haktar65/quarter-tone-keyboard/docs/CAD/QTKB-blocks/V2BL-Layout.stp

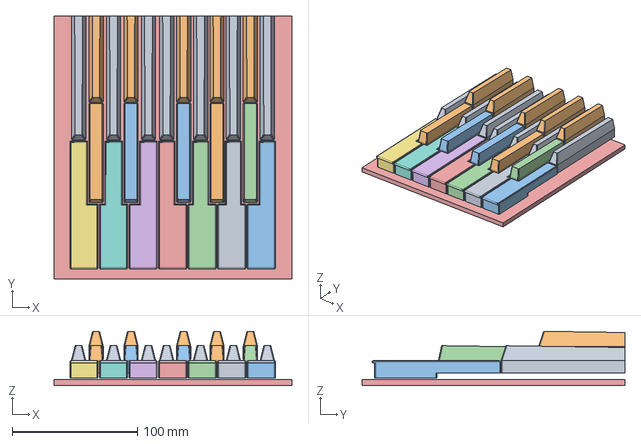
[picture p18: CAD file, 2026-07-05]
docs/CAD/QTKB-blocks/V2BL-Layout.stp
190.0 x 210.0 x 43.4 mm
