haktar65/quarter-tone-keyboard/docs/CAD/_Design/LeversFrontYZ.FCStd

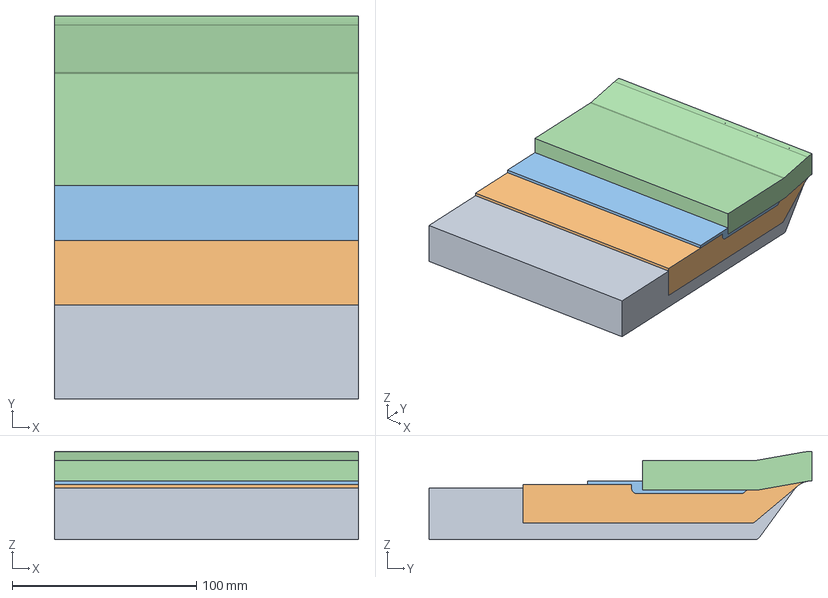
[picture p19: CAD file, 2026-10-06]
docs/CAD/_Design/LeversFrontYZ.FCStd
165.2 x 208.0 x 47.9 mm
bMWTFrontLeverYZ
bMSTFrontLeverYZ
bQWTFrontLeverYZ
bQSTFrontLeverYZ
