haktar65/quarter-tone-keyboard/docs/CAD/QTKB-blocks/PivotCarrier_V0.stp

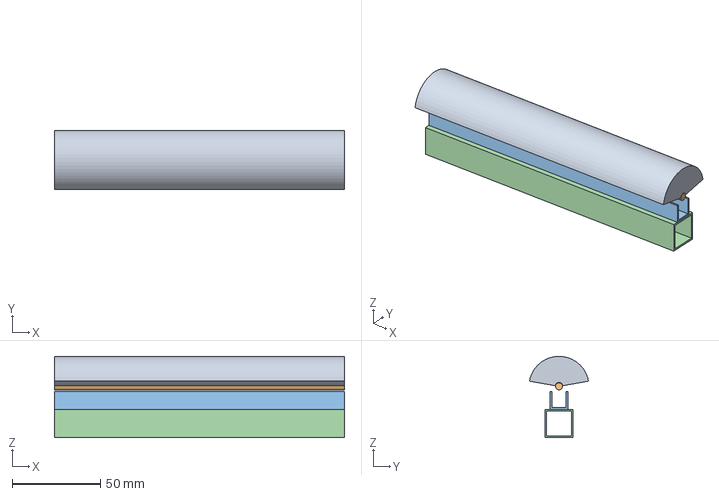
[picture p20: CAD file, 2026-07-05]
docs/CAD/QTKB-blocks/PivotCarrier_V0.stp
164.2 x 33.5 x 46.0 mm
