haktar65/quarter-tone-keyboard/docs/CAD/_Design/LeverRearYZ.FCStd

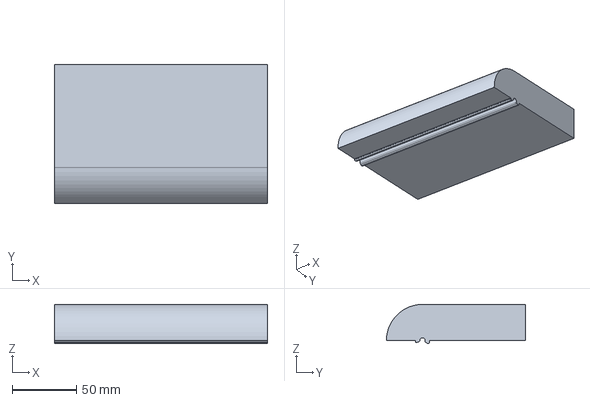
[picture p21: CAD file, 2026-10-06]
docs/CAD/_Design/LeverRearYZ.FCStd
165.2 x 108.0 x 30.4 mm
