haktar65/quarter-tone-keyboard/docs/CAD/QTKB-blocks/YZClrnc_StlPns.stp

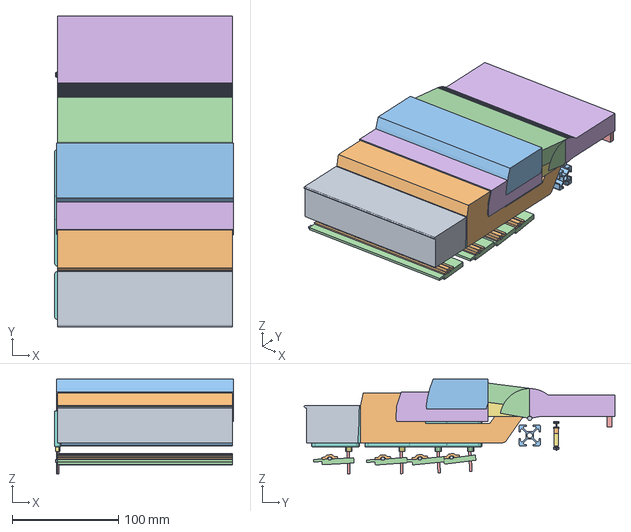
[picture p22: CAD file, 2026-07-05]
docs/CAD/QTKB-blocks/YZClrnc_StlPns.stp
168.2 x 292.0 x 89.2 mm
