haktar65/quarter-tone-keyboard/docs/CAD/_Design/Keys.FCStd

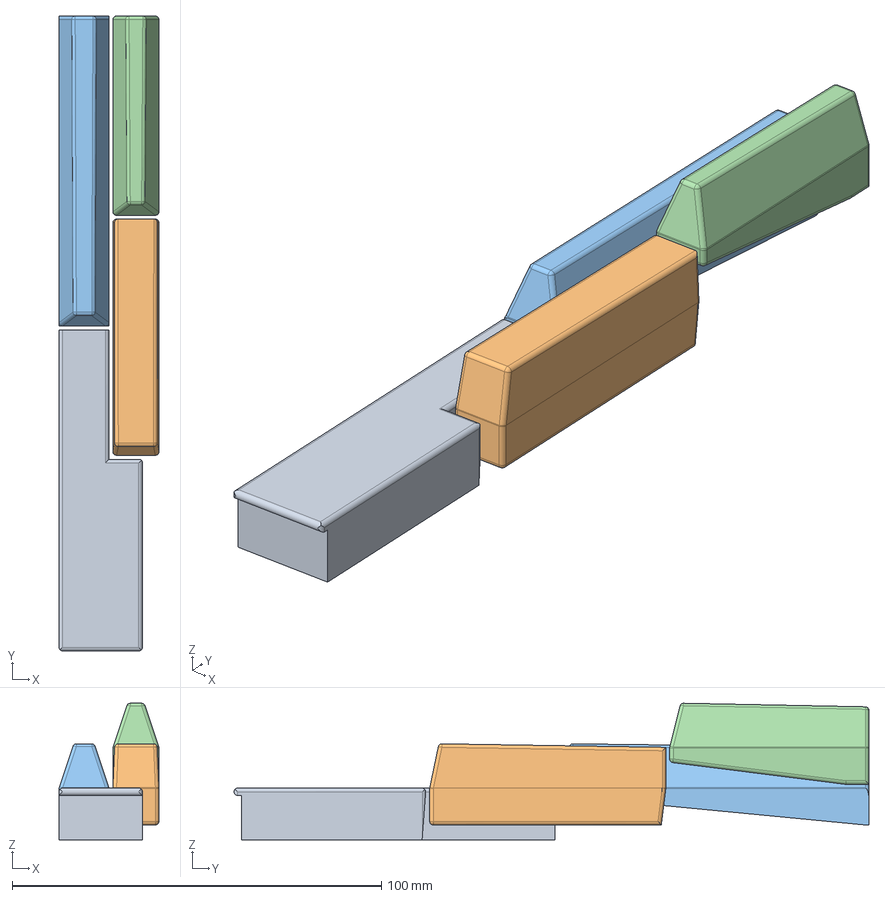
[picture p23: CAD file, 2026-10-06]
docs/CAD/_Design/Keys.FCStd
27.1 x 172.0 x 37.0 mm
bMWTKey
bMSTKey
bQWTKey
bQSTKey
