haktar65/quarter-tone-keyboard/docs/CAD/QTKB-blocks/Klak20.stp

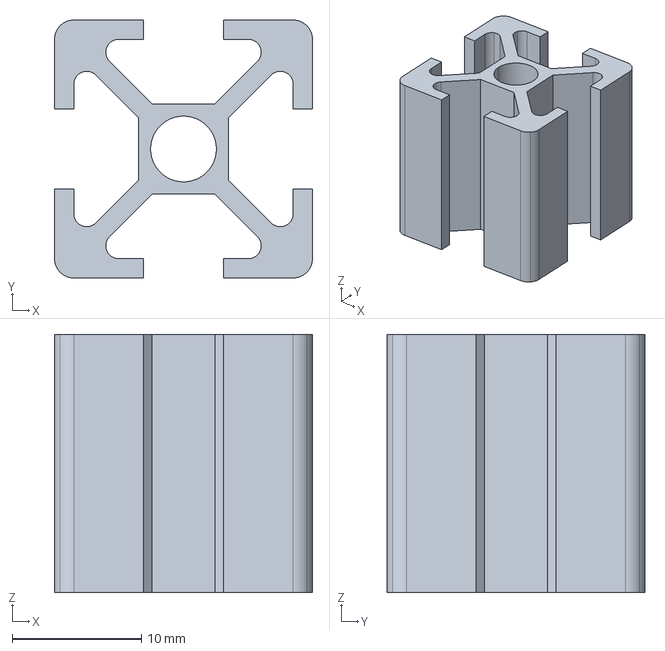
[picture p24: CAD file, 2026-07-05]
docs/CAD/QTKB-blocks/Klak20.stp
20.0 x 20.0 x 20.0 mm
