haktar65/quarter-tone-keyboard/docs/CAD/QTKB-blocks/RctnGrp__SteelV0.stp

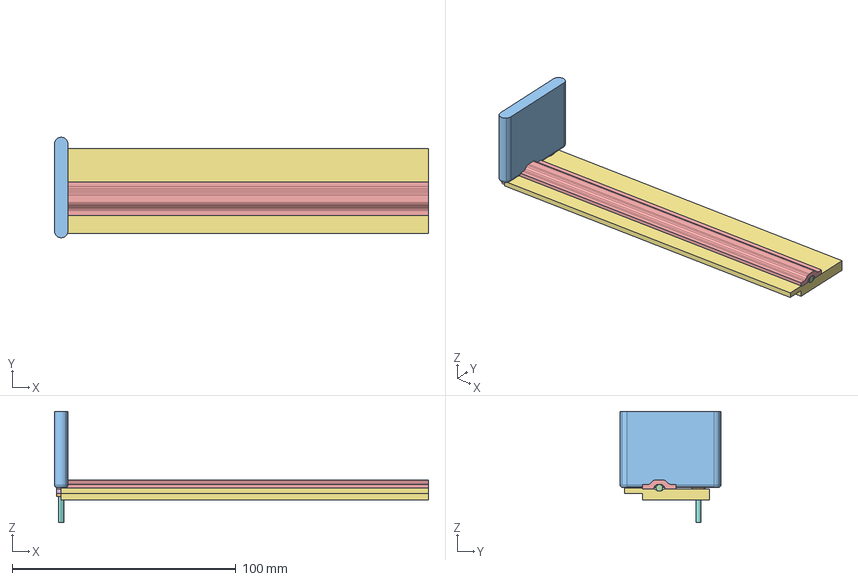
[picture p25: CAD file, 2026-07-05]
docs/CAD/QTKB-blocks/RctnGrp__SteelV0.stp
167.2 x 45.0 x 49.7 mm
