haktar65/quarter-tone-keyboard/docs/CAD/QTKB-blocks/Buffer_V0.stp

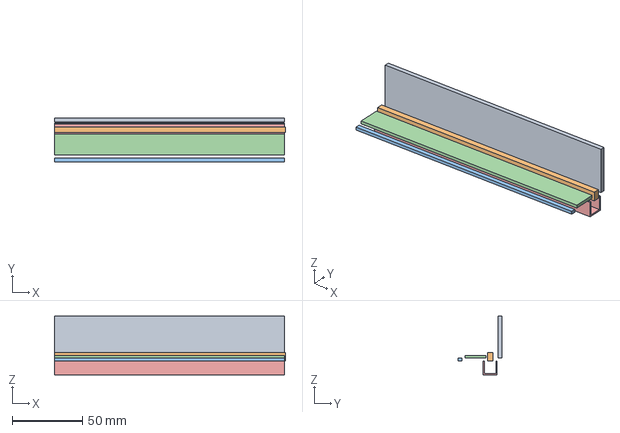
[picture p26: CAD file, 2026-07-05]
docs/CAD/QTKB-blocks/Buffer_V0.stp
165.0 x 31.5 x 42.0 mm
