haktar65/quarter-tone-keyboard/docs/CAD/QTKB-blocks/RctnGrp_BrassV0.stp

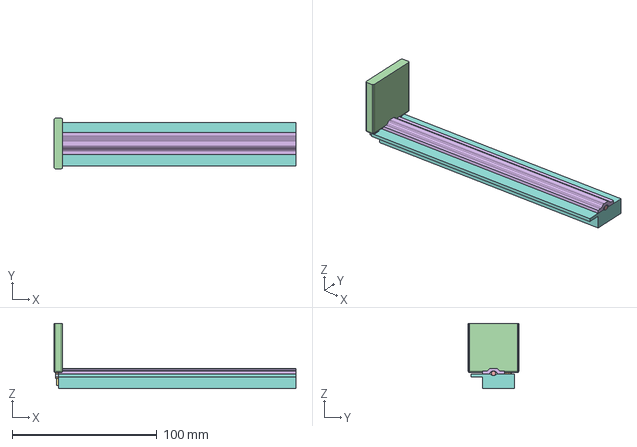
[picture p27: CAD file, 2026-07-05]
docs/CAD/QTKB-blocks/RctnGrp_BrassV0.stp
167.2 x 35.0 x 45.0 mm
