haktar65/quarter-tone-keyboard/docs/CAD/QTKB-blocks/YZClrnc_BrssPns.stp

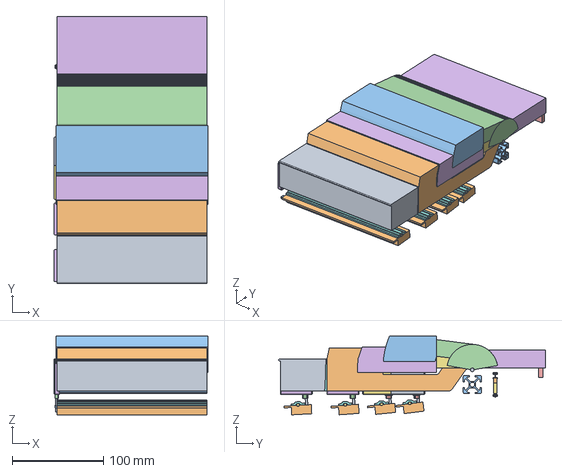
[picture p28: CAD file, 2026-07-05]
docs/CAD/QTKB-blocks/YZClrnc_BrssPns.stp
168.2 x 292.0 x 86.1 mm
