haktar65/quarter-tone-keyboard/docs/CAD/QTKB-blocks/KeysLong.stp

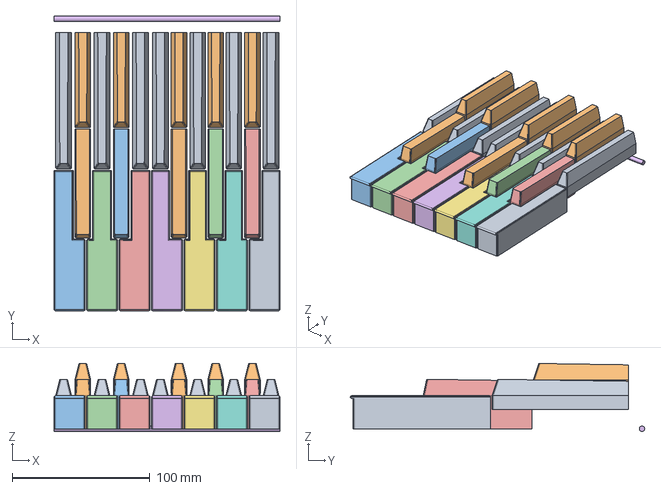
[picture p29: CAD file, 2026-07-05]
docs/CAD/QTKB-blocks/KeysLong.stp
164.2 x 214.0 x 49.4 mm
