haktar65/quarter-tone-keyboard/docs/CAD/QTKB-blocks/X_S_01.stp

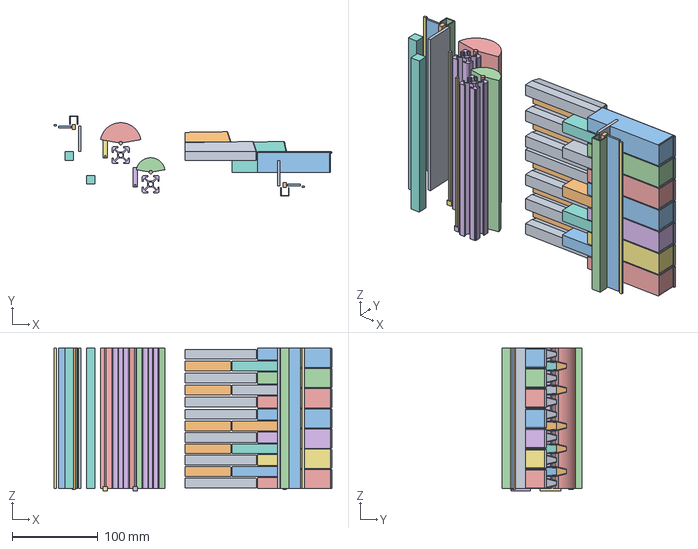
[picture p30: CAD file, 2026-07-05]
docs/CAD/QTKB-blocks/X_S_01.stp
325.0 x 94.0 x 166.7 mm
