haktar65/quarter-tone-keyboard/docs/CAD/QTKB-blocks/X_S_02.stp

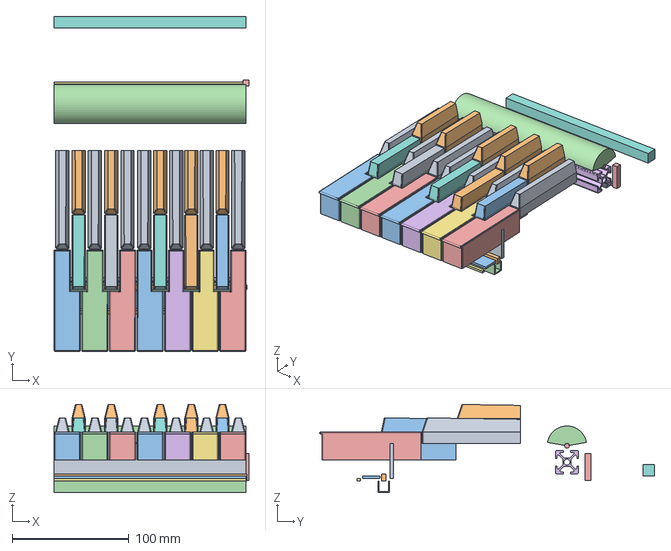
[picture p31: CAD file, 2026-07-05]
docs/CAD/QTKB-blocks/X_S_02.stp
166.7 x 287.0 x 75.4 mm
